PainfulDiodes/z80-breadboard-computer/kicad/z80_UM245R/z80_UM245R.kicad_sch

## KiCad design kicad/z80_UM245R/z80_UM245R.kicad_sch (2024-09-22)

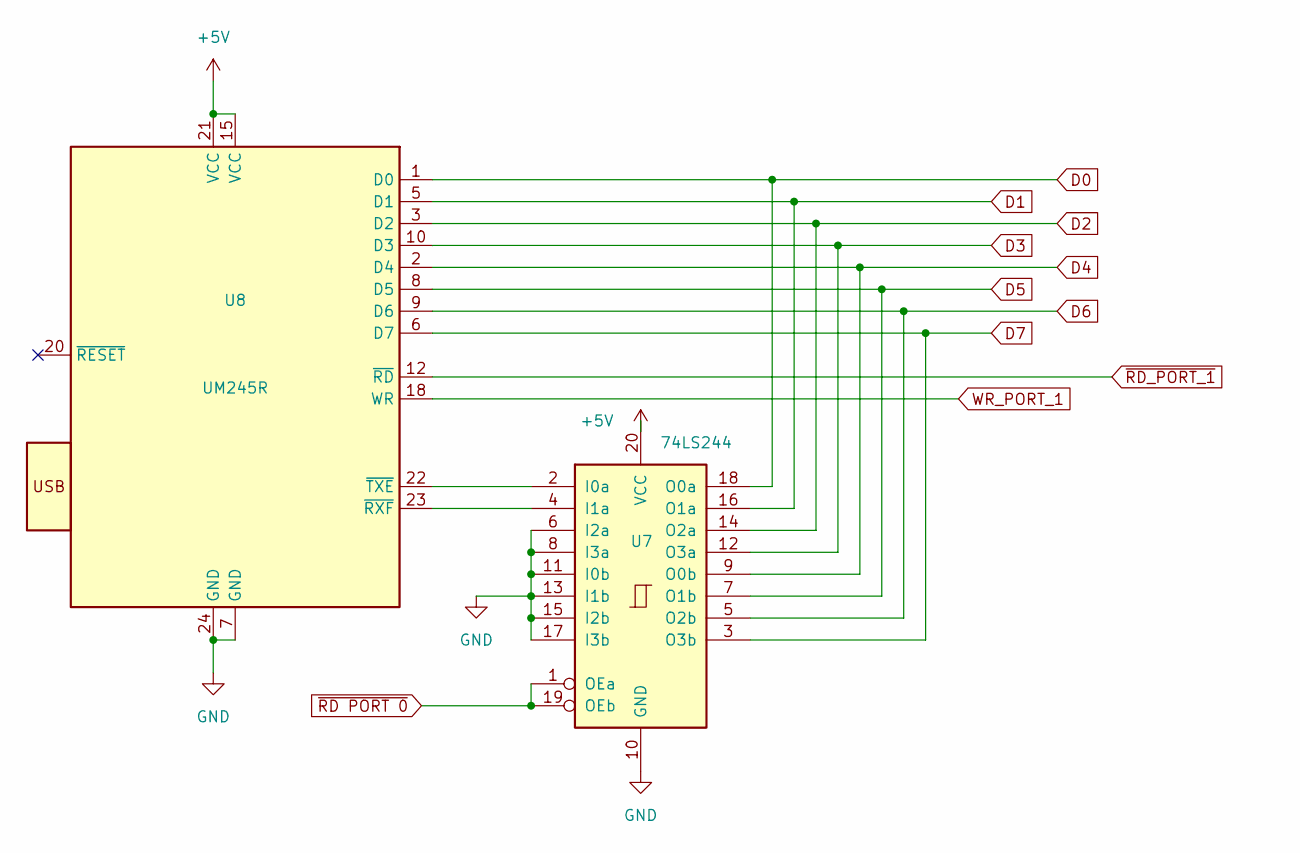
[picture p18: schematic z80_UM245R.kicad_sch]

Parts:
U7: 74LS244
U8: UM245R

Connections:
+5V: U7.20 (VCC), U8.15 (VCC), U8.21 (VCC)
D0: U7.18 (O0a), U8.1 (D0)
D1: U7.16 (O1a), U8.5 (D1)
D2: U7.14 (O2a), U8.3 (D2)
D3: U7.12 (O3a), U8.10 (D3)
D4: U7.9 (O0b), U8.2 (D4)
D5: U7.7 (O1b), U8.8 (D5)
D6: U7.5 (O2b), U8.9 (D6)
D7: U7.3 (O3b), U8.6 (D7)
GND: U7.6 (I2a), U7.8 (I3a), U7.10 (GND), U7.11 (I0b), U7.13 (I1b), U7.15 (I2b), U7.17 (I3b), U8.7 (GND), U8.24 (GND)
unnamed: U7.2 (I0a), U8.22 (~TXE)
unnamed: U7.4 (I1a), U8.23 (~RXF)
WR_PORT_1: U8.18 (WR)
~RD PORT 0: U7.1 (OEa), U7.19 (OEb)
~RD_PORT_1: U8.12 (~RD)
