PainfulDiodes/z80-breadboard-computer/kicad/z80_breadboard/z80_breadboard.kicad_sch

## KiCad design kicad/z80_breadboard/z80_breadboard.kicad_sch (2024-09-22)

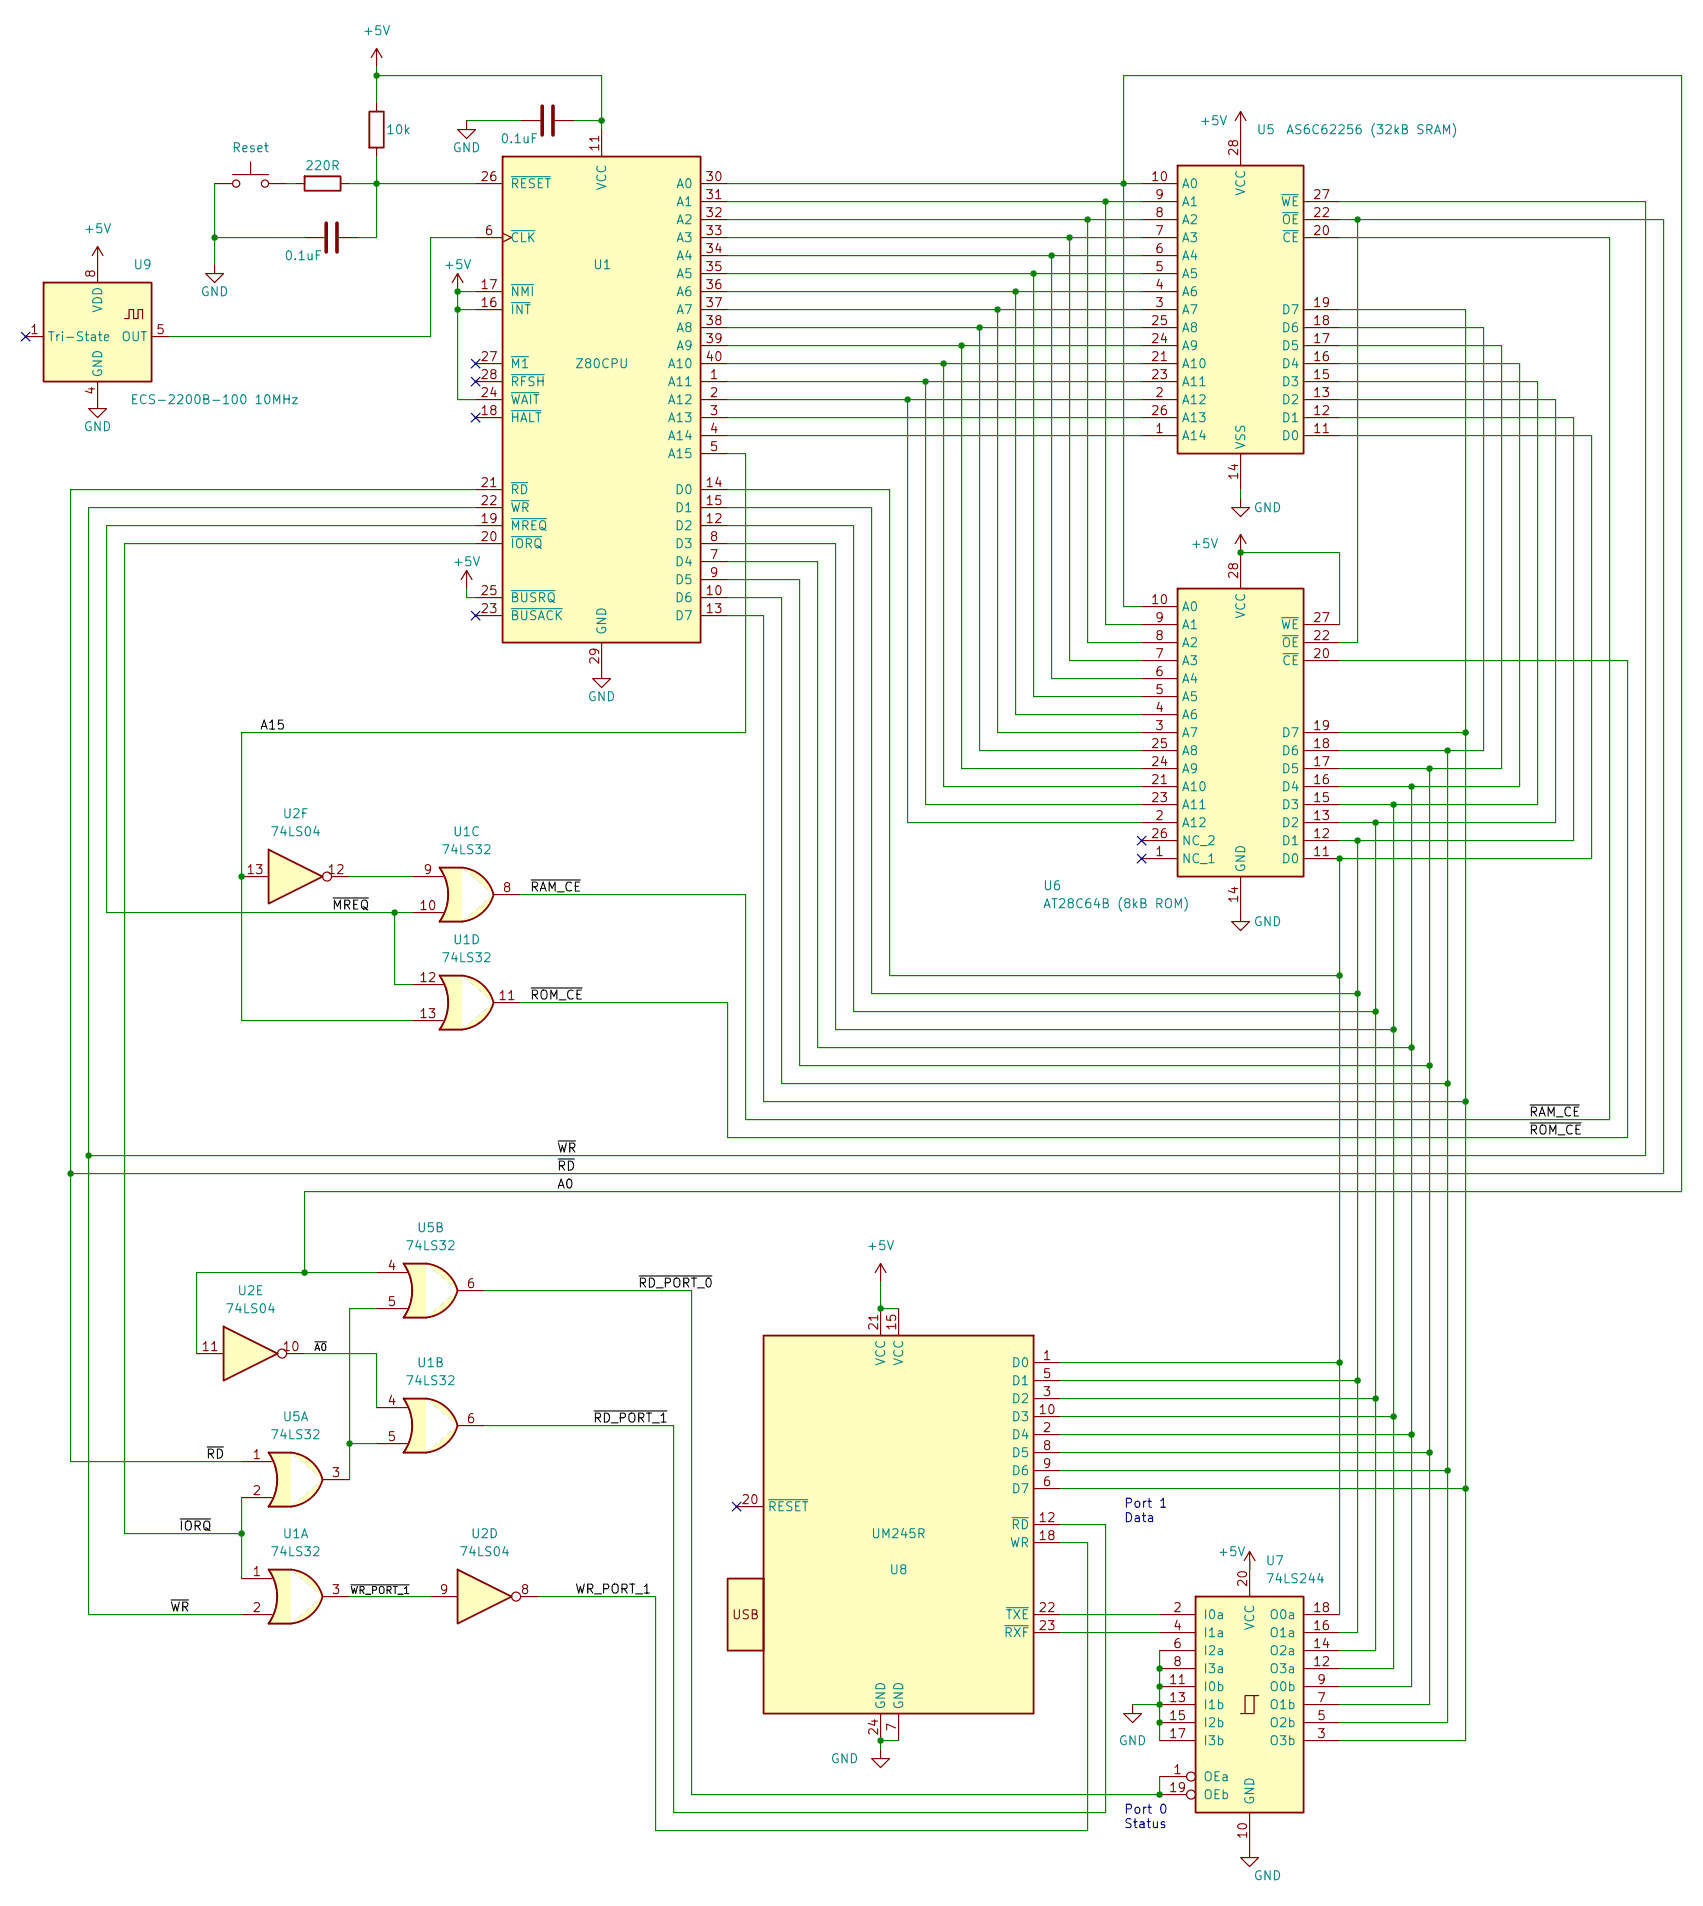
[picture p19: schematic z80_breadboard.kicad_sch]

Parts:
C3, C5: 0.1uF
R1: 10k
R2: 220R
SW1: Reset
U1: Z80CPU
U2: 74LS04
U5: AS6C62256 (32kB SRAM); DIP1587W140P254L3632H381Q28N; Mouser Part Number 913-AS6C62256-55PCN
U6: AT28C64B (8kB ROM); DIP1556W56P254L3702H483Q28N; Mouser Part Number 556-AT28C64B15PU
U7: 74LS244
U8: UM245R
U9: ECS-2200B-100 10MHz; Oscillator_8DIP_ECS_2200x-xxx-4Pin_13.2x13.2mm

Connections:
+5V: C3.1, R1.1, U1.11, U1.16 (~INT), U1.17 (~NMI), U1.24 (~WAIT), U1.25 (~BUSRQ), U5.28 (VCC), U6.27 (~WE), U6.28 (VCC), U7.20 (VCC), U8.15 (VCC), U8.21 (VCC), U9.8 (VDD)
A0: U1.30 (A0), U2.11, U5.4, U5.10, U6.10 (A0)
A15: U1.5, U1.13, U2.13
GND: C3.2, C5.2, SW1.1, U1.29 (GND), U5.14 (VCC), U6.14 (GND), U7.6 (I2a), U7.8 (I3a), U7.10 (GND), U7.11 (I0b), U7.13 (I1b), U7.15 (I2b), U7.17 (I3b), U8.7 (GND), U8.24 (GND), U9.4 (GND)
unnamed: C5.1, R1.2, R2.1, U1.26 (~RESET)
unnamed: R2.2, SW1.2
unnamed: U1.1, U5.23 (A11), U6.23 (A11)
unnamed: U1.2, U5.2, U6.2 (A12)
unnamed: U1.3, U5.26 (A13)
unnamed: U1.4, U5.1
unnamed: U1.5, U5.3, U5.5
unnamed: U1.6, U9.5 (OUT)
unnamed: U1.7 (GND), U5.16 (D4), U6.16 (D4), U7.9 (O0b), U8.2 (D4)
unnamed: U1.8, U5.15 (D3), U6.15 (D3), U7.12 (O3a), U8.10 (D3)
unnamed: U1.9, U2.12, U5.17 (D5), U6.17 (D5), U7.7 (O1b), U8.8 (D5)
unnamed: U1.10, U5.18 (D6), U6.18 (D6), U7.5 (O2b), U8.9 (D6)
unnamed: U1.12, U5.13, U6.13 (D2), U7.14 (O2a), U8.3 (D2)
unnamed: U1.13, U5.19 (D7), U6.19 (D7), U7.3 (O3b), U8.6 (D7)
unnamed: U1.14 (VCC), U5.11, U6.11 (D0), U7.18 (O0a), U8.1 (D0)
unnamed: U1.15 (D1), U5.12, U6.12 (D1), U7.16 (O1a), U8.5 (D1)
unnamed: U1.31 (A1), U5.9, U6.9 (A1)
unnamed: U1.32 (A2), U5.8, U6.8 (A2)
unnamed: U1.33 (A3), U5.7 (GND), U6.7 (A3)
unnamed: U1.34 (A4), U5.6, U6.6 (A4)
unnamed: U1.35 (A5), U5.5, U6.5 (A5)
unnamed: U1.36 (A6), U5.4, U6.4 (A6)
unnamed: U1.37 (A7), U5.3, U6.3 (A7)
unnamed: U1.38 (A8), U5.25 (A8), U6.25 (A8)
unnamed: U1.39 (A9), U5.24 (A9), U6.24 (A9)
unnamed: U1.40 (A10), U5.21 (A10), U6.21 (A10)
unnamed: U7.2 (I0a), U8.22 (~TXE)
unnamed: U7.4 (I1a), U8.23 (~RXF)
WR_PORT_1: U2.8, U8.18 (WR)
~A0: U1.4, U2.10
~IORQ: U1.1, U1.20 (~IORQ), U5.2
~MREQ: U1.10, U1.12, U1.19 (~MREQ)
~RAM_CE: U1.8, U5.20 (~CE)
~RD_PORT_0: U5.6, U7.1 (OEa), U7.19 (OEb)
~RD_PORT_1: U1.6, U8.12 (~RD)
~RD: U1.21 (~RD), U5.1, U5.22 (~OE), U6.22 (~OE)
~ROM_CE: U1.11, U6.20 (~CE)
~WR_PORT_1: U1.3, U2.9
~WR: U1.2, U1.22 (~WR), U5.27 (~WE)

Notes on the sheet:
Port 1 Data
Port 0 Status
