PainfulDiodes/z80-breadboard-computer/kicad/z80_breadboard_hld/z80_breadboard_hld.kicad_sch

## KiCad design kicad/z80_breadboard_hld/z80_breadboard_hld.kicad_sch (2024-09-22)

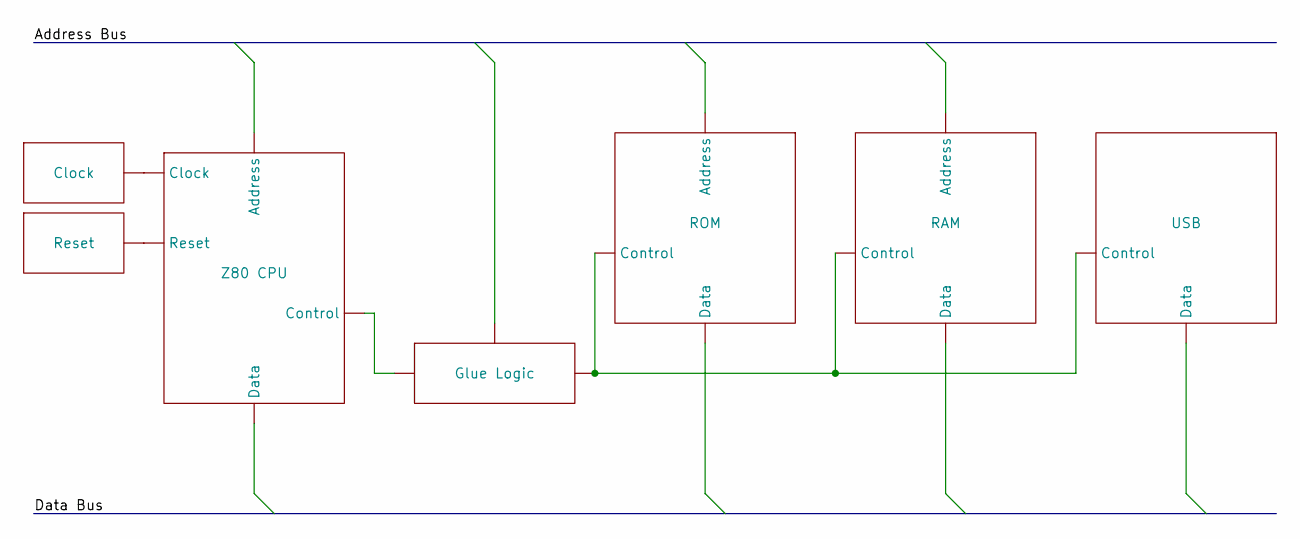
[picture p20: schematic z80_breadboard_hld.kicad_sch]

Parts:
U1: Z80 CPU
U2: Clock
U3: Reset
U4: ROM
U5: RAM
U6: USB
U7: Glue Logic

Connections:
unnamed: U1., U2., U3., U7.
unnamed: U4., U5., U6., U7.
