PainfulDiodes/z80-breadboard-computer/kicad/z80_clock_reset/z80_clock_reset.kicad_sch

## KiCad design kicad/z80_clock_reset/z80_clock_reset.kicad_sch (2024-09-22)

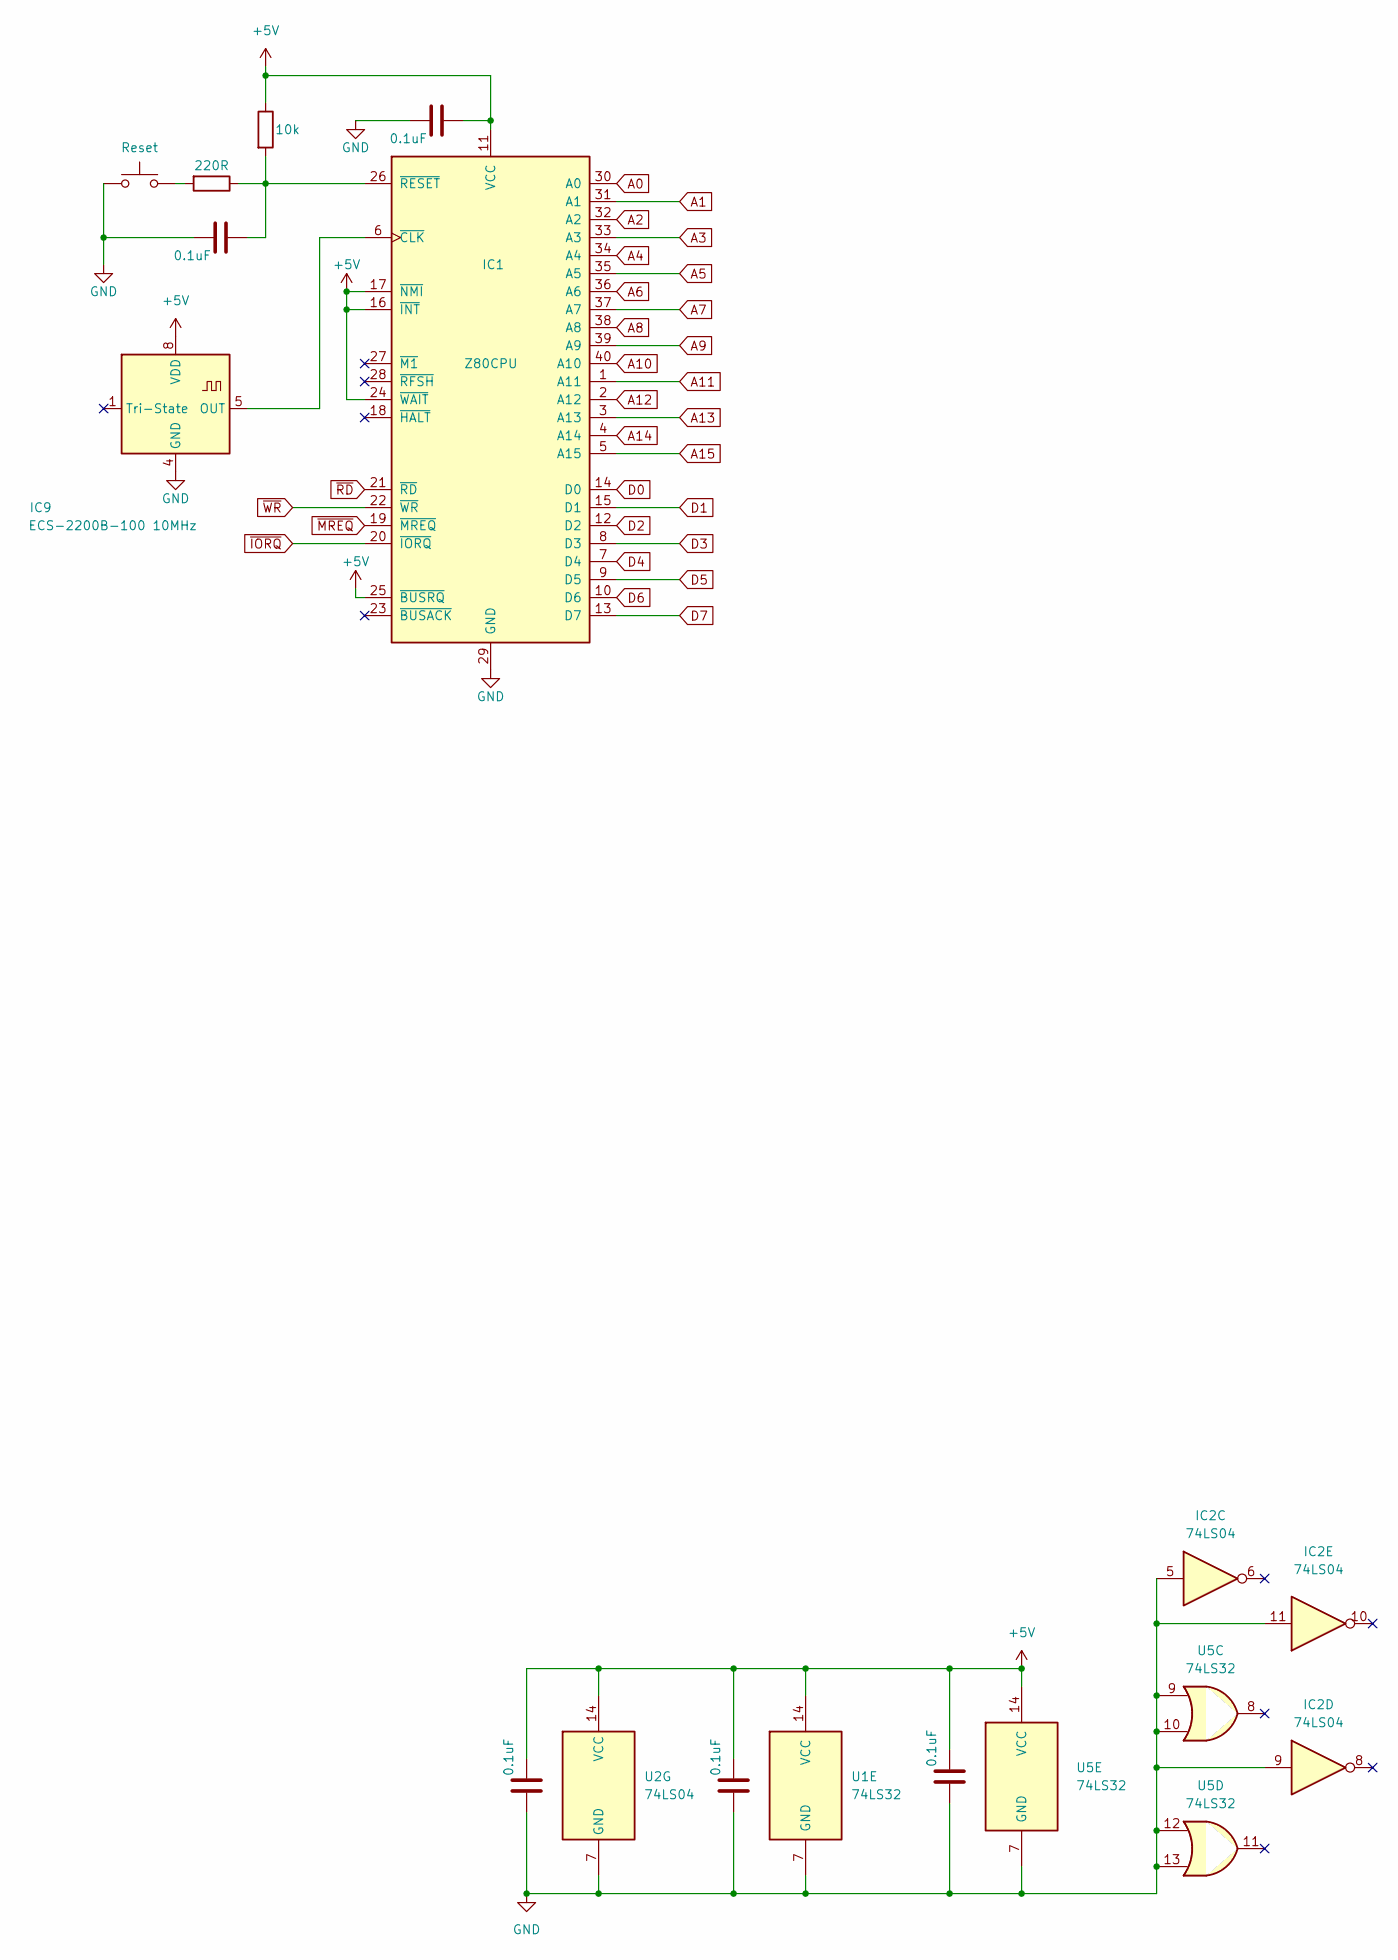
[picture p21: schematic z80_clock_reset.kicad_sch]

Parts:
C1, C2, C3, C4, C5: 0.1uF
IC1: Z80CPU
IC2: 74LS04
IC9: ECS-2200B-100 10MHz; Oscillator_8DIP_ECS_2200x-xxx-4Pin_13.2x13.2mm
R1: 10k
R2: 220R
SW1: Reset
U1, U5: 74LS32
U2: 74LS04

Connections:
+5V: C1.2, C2.2, C3.1, C4.2, IC1.11 (VCC), IC1.16 (~INT), IC1.17 (~NMI), IC1.24 (~WAIT), IC1.25 (~BUSRQ), IC9.8 (VDD), R1.1, U1.14 (VCC), U2.14 (VCC), U5.14 (VCC)
A0: IC1.30 (A0)
A1: IC1.31 (A1)
A2: IC1.32 (A2)
A3: IC1.33 (A3)
A4: IC1.34 (A4)
A5: IC1.35 (A5)
A6: IC1.36 (A6)
A7: IC1.37 (A7)
A8: IC1.38 (A8)
A9: IC1.39 (A9)
A10: IC1.40 (A10)
A11: IC1.1 (A11)
A12: IC1.2 (A12)
A13: IC1.3 (A13)
A14: IC1.4 (A14)
A15: IC1.5 (A15)
D0: IC1.14 (D0)
D1: IC1.15 (D1)
D2: IC1.12 (D2)
D3: IC1.8 (D3)
D4: IC1.7 (D4)
D5: IC1.9 (D5)
D6: IC1.10 (D6)
D7: IC1.13 (D7)
GND: C1.1, C2.1, C3.2, C4.1, C5.2, IC1.29 (GND), IC2.5, IC2.9, IC2.11, IC9.4 (GND), SW1.1, U1.7 (GND), U2.7 (GND), U5.7 (GND), U5.9, U5.10, U5.12, U5.13
unnamed: C5.1, IC1.26 (~RESET), R1.2, R2.1
unnamed: IC1.6 (~CLK), IC9.5 (OUT)
unnamed: R2.2, SW1.2
~IORQ: IC1.20 (~IORQ)
~MREQ: IC1.19 (~MREQ)
~RD: IC1.21 (~RD)
~WR: IC1.22 (~WR)
