PainfulDiodes/z80-breadboard-computer/kicad/z80_glue_logic/z80_glue_logic.kicad_sch

## KiCad design kicad/z80_glue_logic/z80_glue_logic.kicad_sch (2024-09-22)

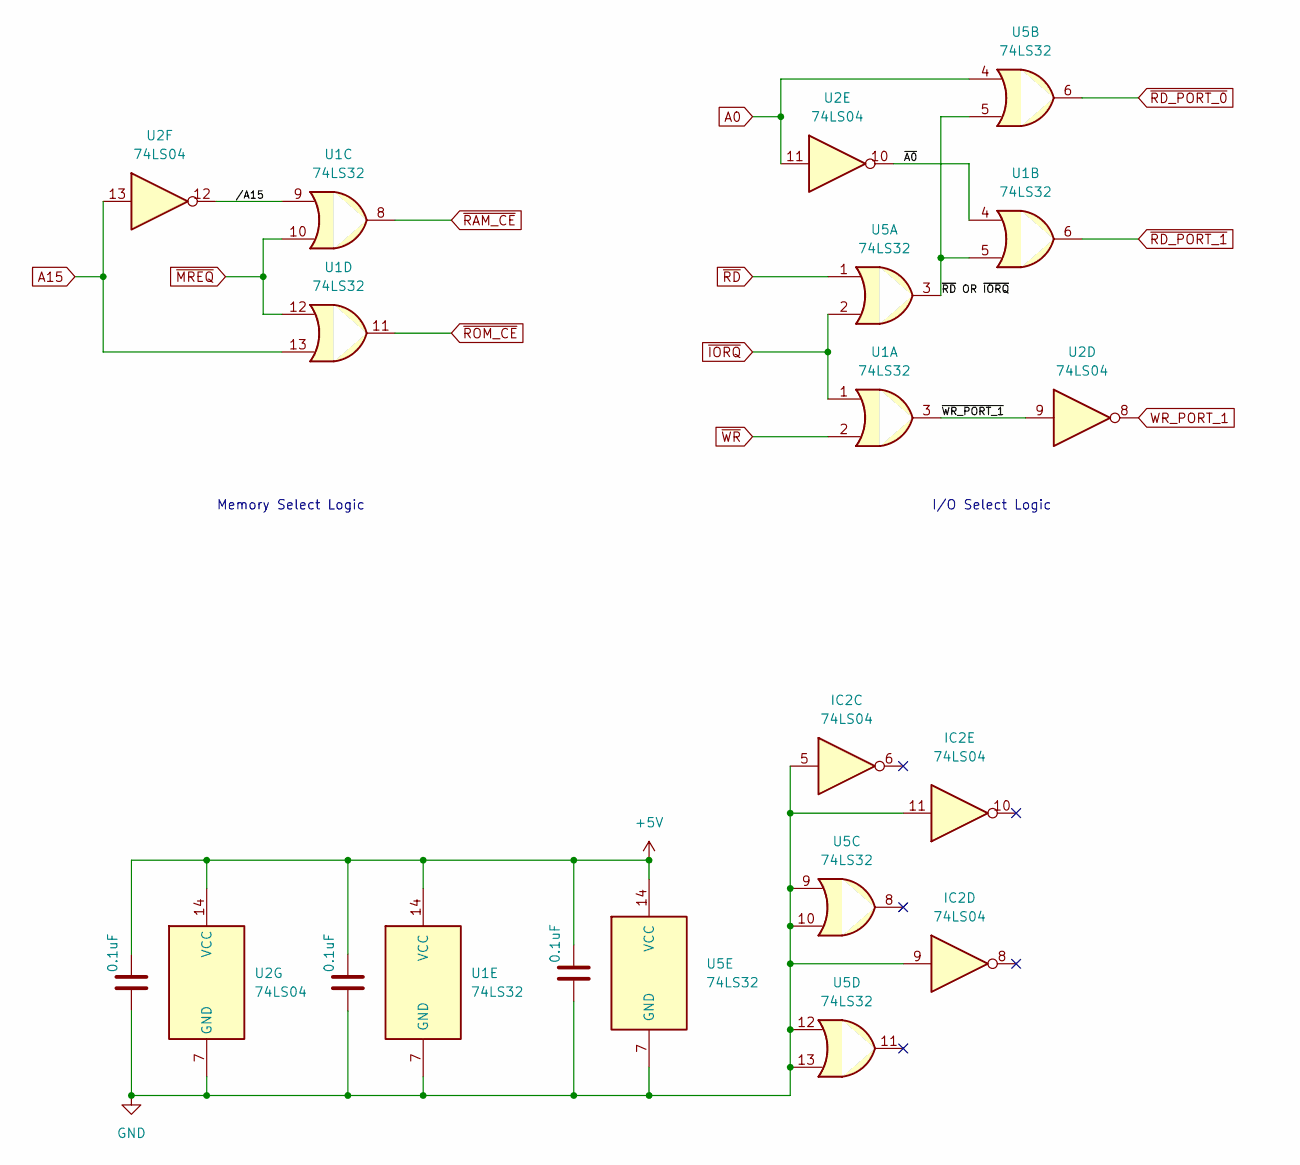
[picture p22: schematic z80_glue_logic.kicad_sch]

Parts:
C1, C2, C4: 0.1uF
IC2: 74LS04
U1, U5: 74LS32
U2: 74LS04

Connections:
+5V: C1.2, C2.2, C4.2, U1.14 (VCC), U2.14 (VCC), U5.14 (VCC)
A0: U2.11, U5.4
A15: U1.13, U2.13
GND: C1.1, C2.1, C4.1, IC2.5, IC2.9, IC2.11, U1.7 (GND), U2.7 (GND), U5.7 (GND), U5.9, U5.10, U5.12, U5.13
WR_PORT_1: U2.8
/A15: U1.9, U2.12
~A0: U1.4, U2.10
~IORQ: U1.1, U5.2
~MREQ: U1.10, U1.12
~RAM_CE: U1.8
~RD_PORT_0: U5.6
~RD_PORT_1: U1.6
~RD: U5.1
~RD OR ~IORQ: U1.5, U5.3, U5.5
~ROM_CE: U1.11
~WR_PORT_1: U1.3, U2.9
~WR: U1.2

Notes on the sheet:
Memory Select Logic
I/O Select Logic
