PainfulDiodes/z80-breadboard-computer/kicad/z80_memory/z80_memory.kicad_sch

## KiCad design kicad/z80_memory/z80_memory.kicad_sch (2024-09-22)

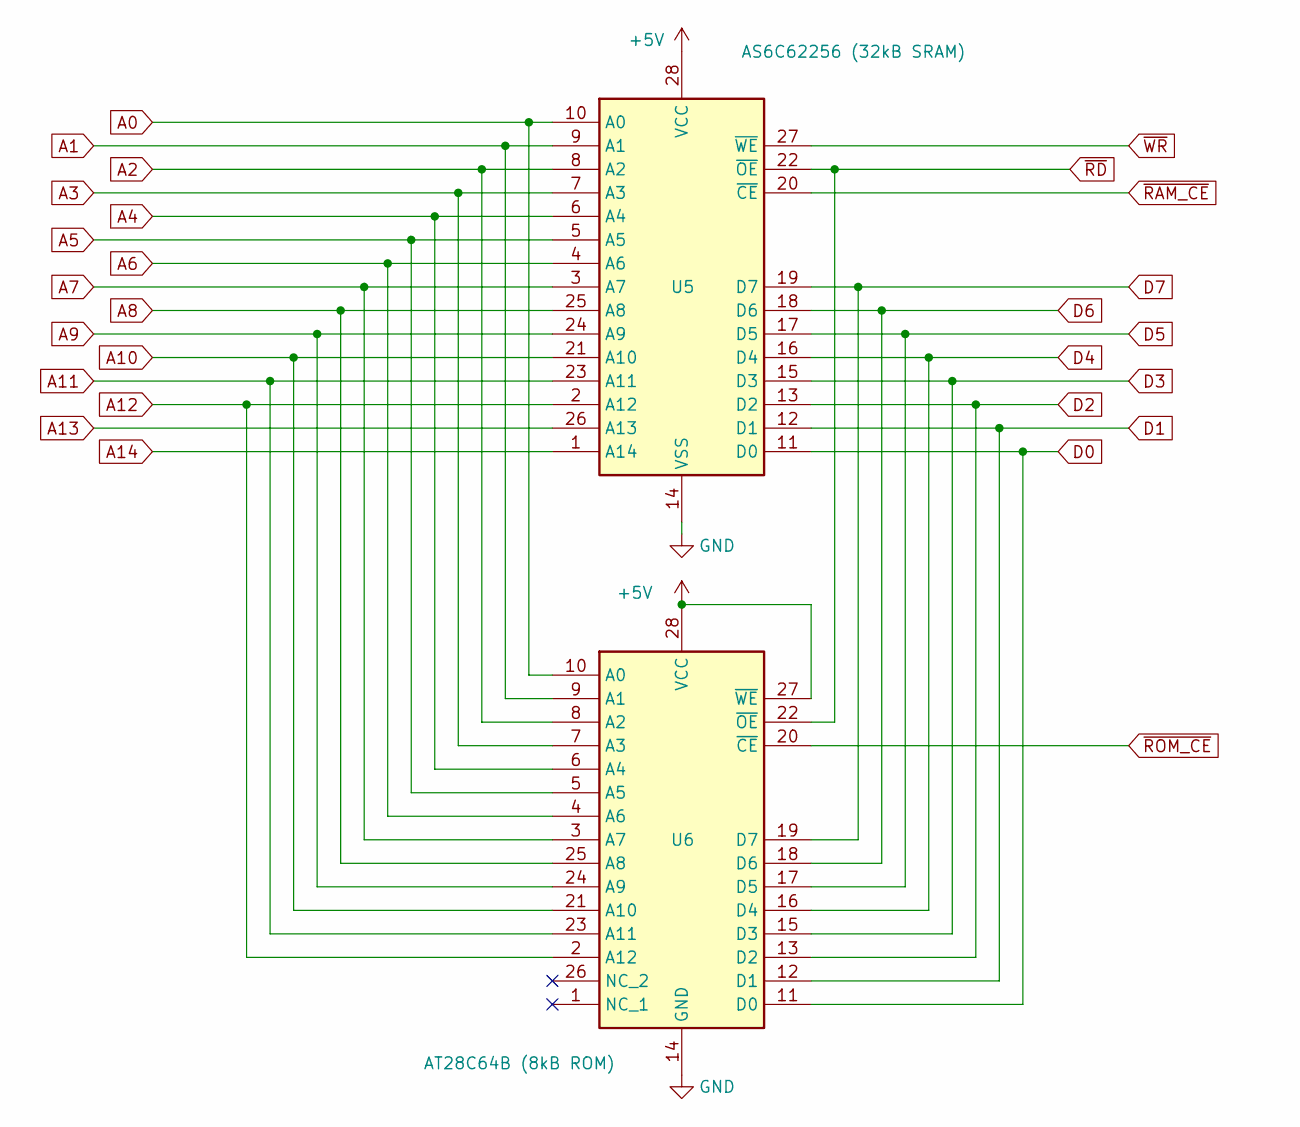
[picture p23: schematic z80_memory.kicad_sch]

Parts:
U5: AS6C62256 (32kB SRAM); DIP1587W140P254L3632H381Q28N; Mouser Part Number 913-AS6C62256-55PCN
U6: AT28C64B (8kB ROM); DIP1556W56P254L3702H483Q28N; Mouser Part Number 556-AT28C64B15PU

Connections:
+5V: U5.28 (VCC), U6.27 (~WE), U6.28 (VCC)
A0: U5.10 (A0), U6.10 (A0)
A1: U5.9 (A1), U6.9 (A1)
A2: U5.8 (A2), U6.8 (A2)
A3: U5.7 (A3), U6.7 (A3)
A4: U5.6 (A4), U6.6 (A4)
A5: U5.5 (A5), U6.5 (A5)
A6: U5.4 (A6), U6.4 (A6)
A7: U5.3 (A7), U6.3 (A7)
A8: U5.25 (A8), U6.25 (A8)
A9: U5.24 (A9), U6.24 (A9)
A10: U5.21 (A10), U6.21 (A10)
A11: U5.23 (A11), U6.23 (A11)
A12: U5.2 (A12), U6.2 (A12)
A13: U5.26 (A13)
A14: U5.1 (A14)
D0: U5.11 (D0), U6.11 (D0)
D1: U5.12 (D1), U6.12 (D1)
D2: U5.13 (D2), U6.13 (D2)
D3: U5.15 (D3), U6.15 (D3)
D4: U5.16 (D4), U6.16 (D4)
D5: U5.17 (D5), U6.17 (D5)
D6: U5.18 (D6), U6.18 (D6)
D7: U5.19 (D7), U6.19 (D7)
GND: U5.14 (VSS), U6.14 (GND)
~RAM_CE: U5.20 (~CE)
~RD: U5.22 (~OE), U6.22 (~OE)
~ROM_CE: U6.20 (~CE)
~WR: U5.27 (~WE)
